sparkfun/SparkFun_IoT_Node_LoRaWAN/docs/assets/img/Digi-XON-GetStarted.png

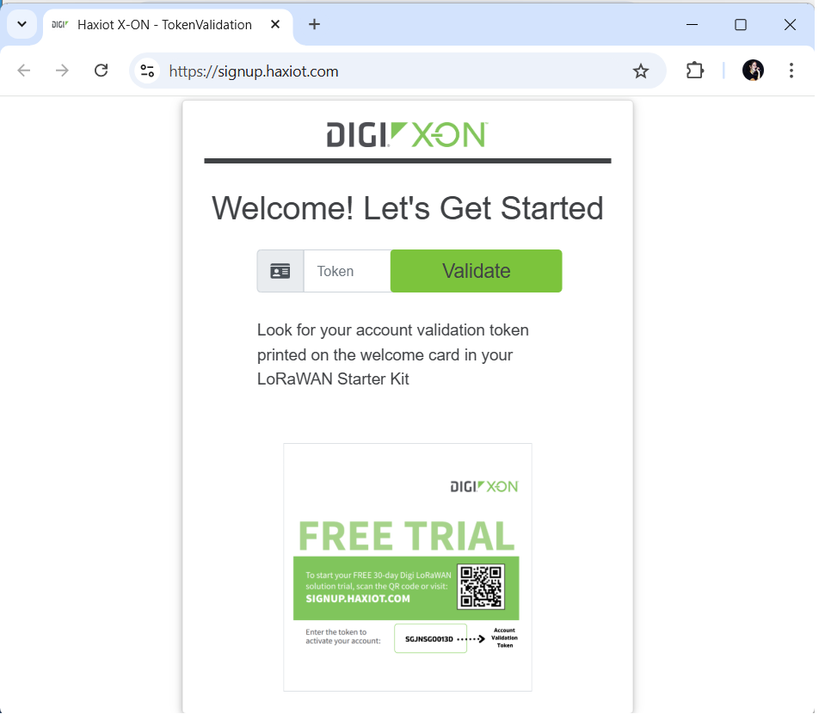
docs/assets/img/Digi-XON-GetStarted.png
