sparkfun/SparkFun_IoT_Node_LoRaWAN/docs/assets/img/Digi-XON-LoginPage.png

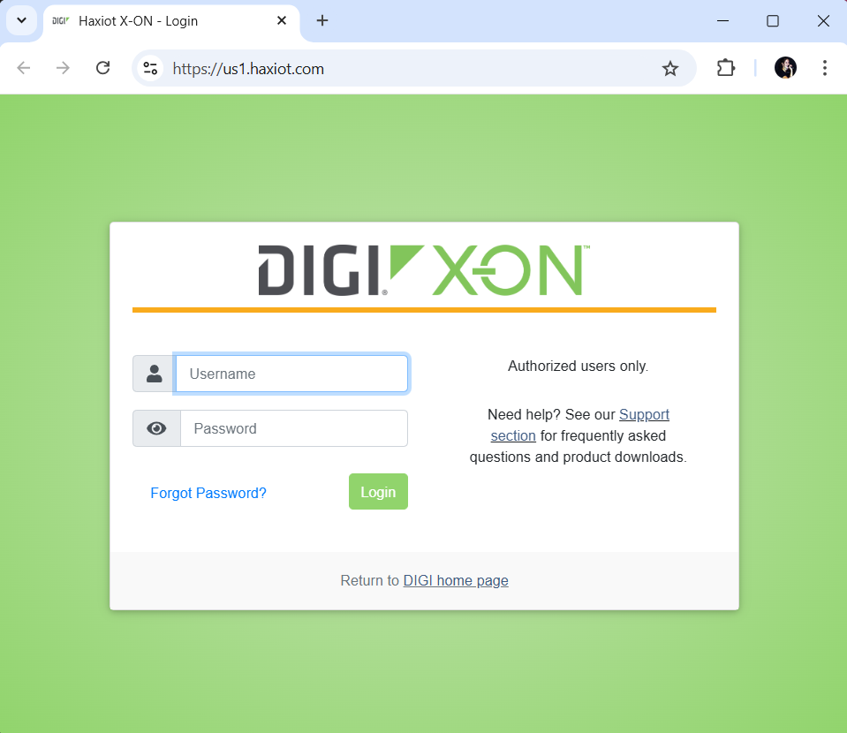
docs/assets/img/Digi-XON-LoginPage.png
