sparkfun/SparkFun_IoT_Node_LoRaWAN/docs/assets/img/ScanningPageInitial.png

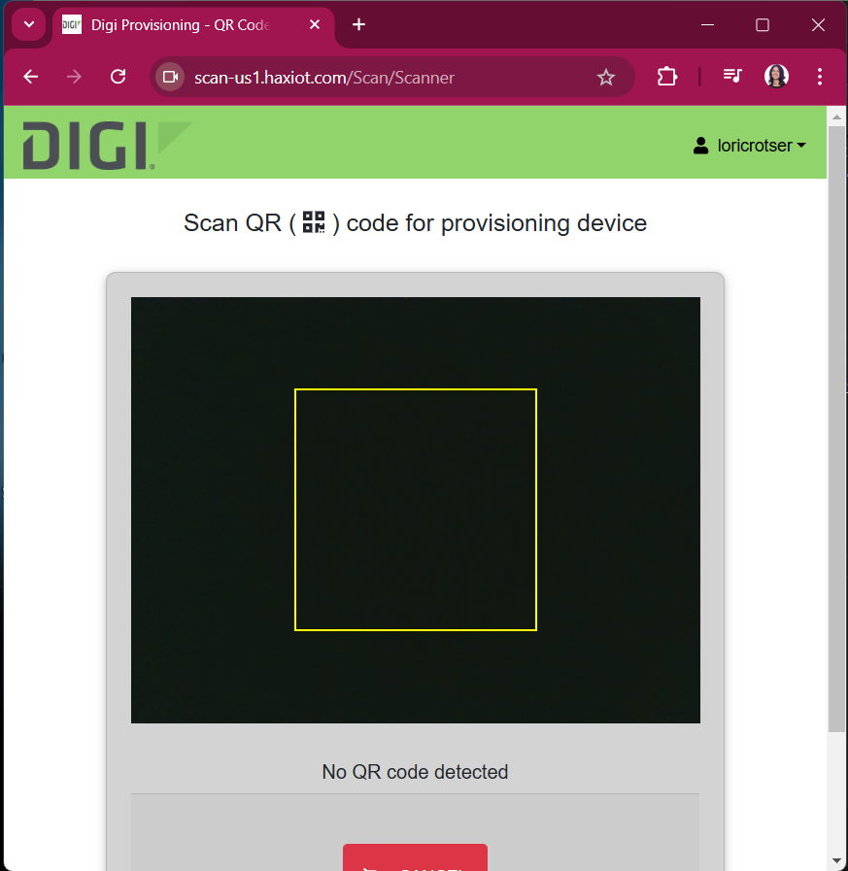
docs/assets/img/ScanningPageInitial.png
