sparkfun/SparkFun_IoT_Node_LoRaWAN/docs/assets/img/SparkFun_IoT_Node_LoRaWAN.jpg

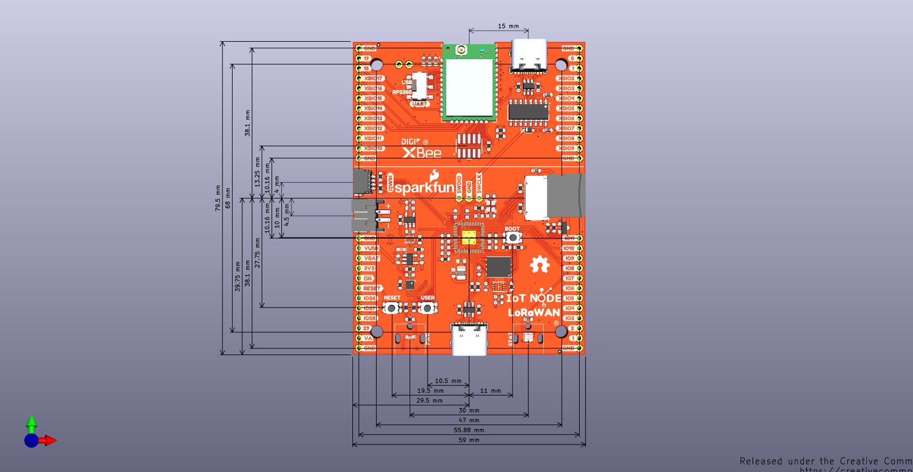
docs/assets/img/SparkFun_IoT_Node_LoRaWAN.jpg
