sparkfun/SparkFun_IoT_Node_LoRaWAN/docs/assets/img/TeraTerm_Connecting.png

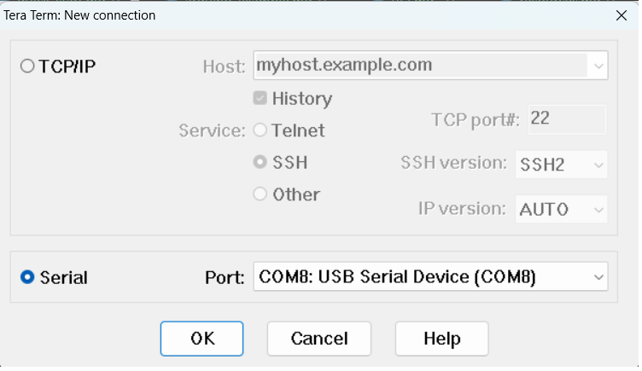
docs/assets/img/TeraTerm_Connecting.png
