sparkfun/SparkFun_IoT_Node_LoRaWAN/docs/assets/img/teraterm_sendingImages.png

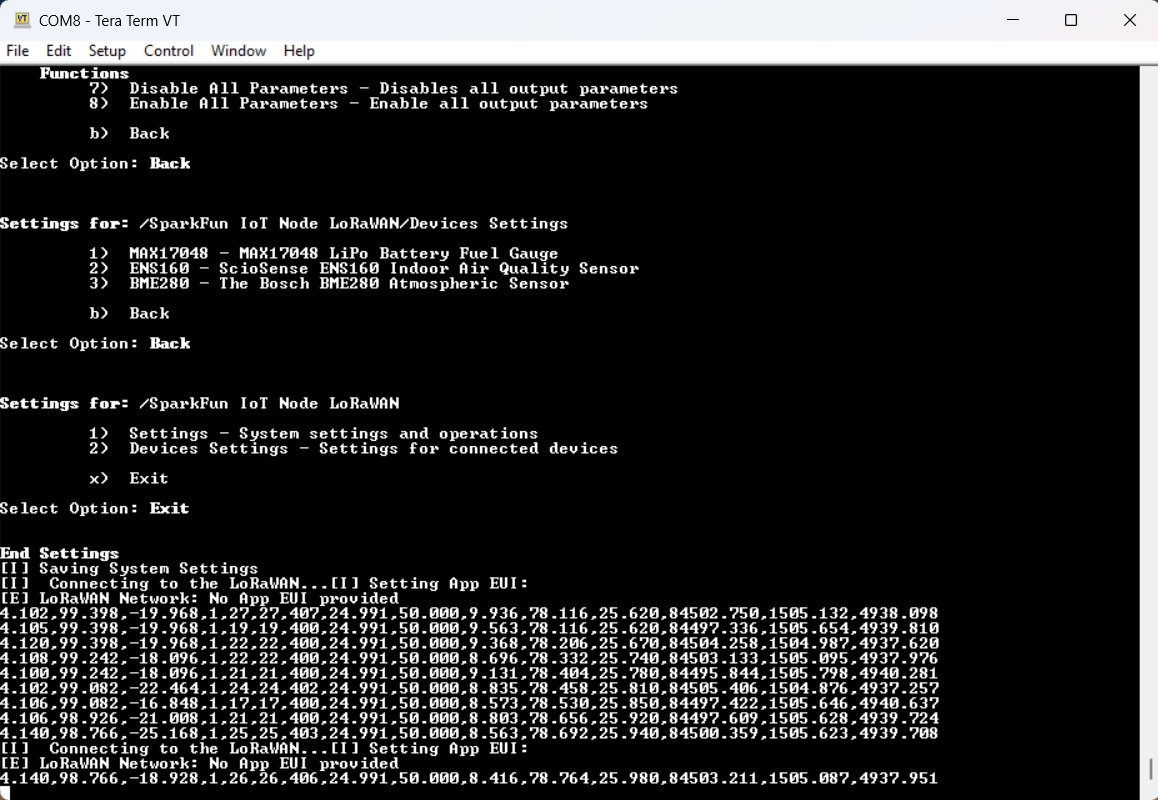
docs/assets/img/teraterm_sendingImages.png
