sparkfun/SparkFun_IoT_Node_LoRaWAN/docs/assets/img/X-OnActivationPage.png

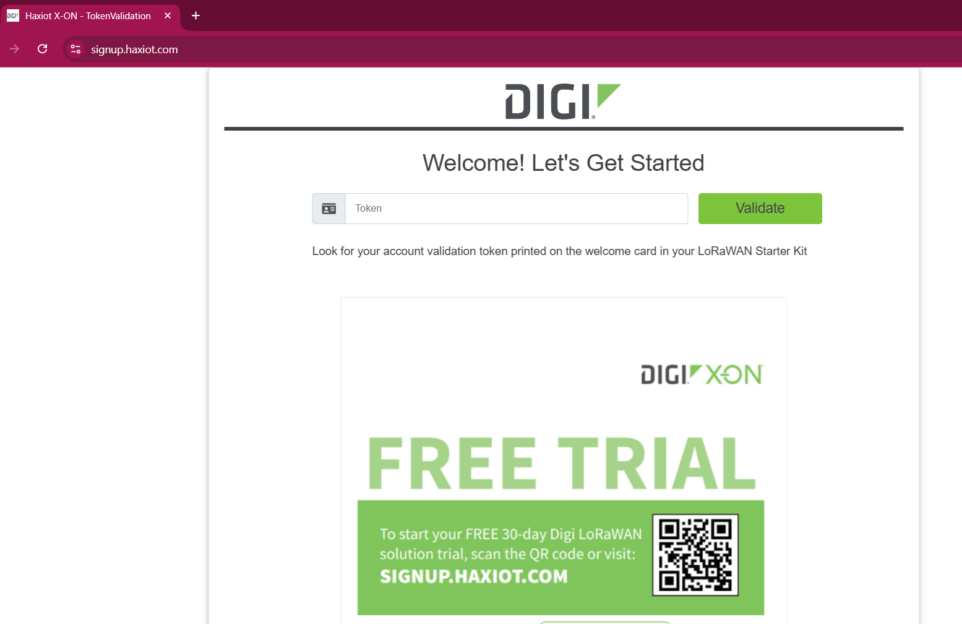
docs/assets/img/X-OnActivationPage.png
